UnHolds/BeerTracker/code/src/icons.h

#ifndef ICONS_H
#define ICONS_H

#include <Arduino.h>

// 'beer', 32x32px
static const unsigned char bitmap_beer [] PROGMEM = {
	0x00, 0xe1, 0xf0, 0x00, 0x03, 0xf3, 0xfc, 0x00, 0x03, 0xbf, 0xfe, 0x00, 0x1f, 0xff, 0xee, 0x00,
	0x3f, 0xff, 0xff, 0x00, 0x3f, 0xff, 0xff, 0x00, 0x7f, 0xff, 0xff, 0x00, 0x7d, 0xfc, 0x03, 0x00,
	0x7e, 0x38, 0x01, 0x00, 0x74, 0x00, 0x01, 0x00, 0x7c, 0xc6, 0x31, 0xfc, 0x38, 0xc6, 0x31, 0x02,
	0x08, 0xc6, 0x31, 0x01, 0x08, 0xc6, 0x31, 0xf1, 0x08, 0xc6, 0x31, 0x09, 0x08, 0xc6, 0x31, 0x09,
	0x08, 0xc6, 0x31, 0x09, 0x08, 0xc6, 0x31, 0x09, 0x08, 0xc6, 0x31, 0x09, 0x08, 0xc6, 0x31, 0x09,
	0x08, 0xc6, 0x31, 0x09, 0x08, 0xc6, 0x31, 0x09, 0x08, 0xc6, 0x31, 0x09, 0x08, 0xc6, 0x31, 0xf1,
	0x08, 0xc6, 0x31, 0x01, 0x08, 0xc6, 0x31, 0x02, 0x08, 0xc6, 0x31, 0xfc, 0x08, 0xc6, 0x31, 0x00,
	0x08, 0x00, 0x01, 0x00, 0x08, 0x00, 0x01, 0x00, 0x08, 0x00, 0x01, 0x00, 0x07, 0xff, 0xfe, 0x00
};
// 'shot', 32x32px
static const unsigned char bitmap_shot [] PROGMEM = {
	0x00, 0x00, 0x00, 0x00, 0x00, 0x00, 0x00, 0x00, 0x00, 0x00, 0x00, 0x00, 0x00, 0x00, 0x00, 0x00,
	0x00, 0x00, 0x00, 0x00, 0x20, 0x00, 0x00, 0x04, 0x20, 0x00, 0x00, 0x04, 0x2f, 0xff, 0xff, 0xf4,
	0x2f, 0xff, 0xff, 0xf4, 0x17, 0xff, 0xff, 0xe8, 0x17, 0xff, 0xff, 0xe8, 0x17, 0xff, 0xff, 0xe8,
	0x0b, 0xff, 0xff, 0xd0, 0x0b, 0xff, 0xff, 0xd0, 0x0b, 0xff, 0xff, 0xd0, 0x0b, 0xff, 0xff, 0xd0,
	0x0b, 0xff, 0xff, 0xd0, 0x0b, 0xff, 0xff, 0xd0, 0x05, 0xff, 0xff, 0xa0, 0x05, 0xff, 0xff, 0xa0,
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
};
// 'crown', 13x10px
static const unsigned char bitmap_crown_cat [] PROGMEM = {
	0xc2, 0x18, 0xa5, 0x28, 0xa5, 0x28, 0x98, 0xc8, 0x80, 0x08, 0xa2, 0x28, 0xa2, 0x28, 0xa2, 0x28,
	0x80, 0x08, 0x7f, 0xf0
};

// 'crown', 22x17px
static const unsigned char bitmap_crown [] PROGMEM = {
	0xc0, 0x30, 0x0c, 0xa0, 0x48, 0x14, 0x90, 0x48, 0x24, 0x90, 0x84, 0x24, 0x88, 0x84, 0x44, 0x89,
	0x02, 0x44, 0x86, 0x01, 0x84, 0xb0, 0xcc, 0x34, 0xb0, 0xcc, 0x34, 0x80, 0x00, 0x04, 0x80, 0x00,
	0x04, 0xb3, 0x33, 0x34, 0xb3, 0x33, 0x34, 0xb3, 0x33, 0x34, 0x80, 0x00, 0x04, 0x40, 0x00, 0x08,
	0x3f, 0xff, 0xf0
};

#define IMG_ID(id, x_size, y_size) x_size << 16 | y_size << 8 | id

enum class Icon {
    BEER = IMG_ID(0, 32, 32),
    SHOT = IMG_ID(1, 32, 32),
    TIME = IMG_ID(2, 32, 32),
    USER_SEL = IMG_ID(3, 32, 32),
    WATER = IMG_ID(4, 32, 32),
    USER = IMG_ID(5, 32, 32),
    BAT = IMG_ID(6, 13, 8),
    LOCKED = IMG_ID(7, 32, 32),
    CAT = IMG_ID(8, 22, 15),
    RANK = IMG_ID(9, 31, 23),
    RESET = IMG_ID(10, 32, 32),
    CROWN_CAT = IMG_ID(11, 13, 10),
    CROWN = IMG_ID(12, 22, 17),
};


#define NUM_ICONS 13
static const unsigned char* icon_array[NUM_ICONS] = {
	bitmap_beer,
	bitmap_shot,
	bitmap_time,
	bitmap_user_sel,
	bitmap_water,
    bitmap_user,
    bitmap_bat,
    bitmap_locked,
    bitmap_cat,
    bitmap_rank,
    bitmap_reset,
    bitmap_crown_cat,
    bitmap_crown
};

#endif
