UnHolds/BeerTracker/code/src/peers.h

#ifndef PEERS_H
#define PEERS_H

#include <Arduino.h>

#define NUMBER_OF_PEERS 7

uint8_t peer_1[] = {0x34, 0x5F, 0x45, 0x37, 0x8C, 0x6C}; // 1
uint8_t peer_2[] = {0x34, 0x5F, 0x45, 0x38, 0xED, 0xA4}; // 2
uint8_t peer_3[] = {0xEC, 0xC9, 0xFF, 0xB8, 0x79, 0xA0}; // 3
uint8_t peer_4[] = {0x34, 0x5F, 0x45, 0x37, 0x8C, 0xB0}; // 4
uint8_t peer_5[] = {0x34, 0x5F, 0x45, 0x37, 0x84, 0x7C}; // 5
uint8_t peer_6[] = {0x34, 0x5F, 0x45, 0x37, 0x8B, 0x2C}; // 6
uint8_t peer_7[] = {0xEC, 0xC9, 0xFF, 0xB8, 0x7B, 0x68}; // 7

uint8_t* peers[] = {peer_1, peer_2, peer_3, peer_4, peer_5, peer_6, peer_7};

#endif
